osakechan/notoriousPID/img/LCD/nPIDmenu.jpg

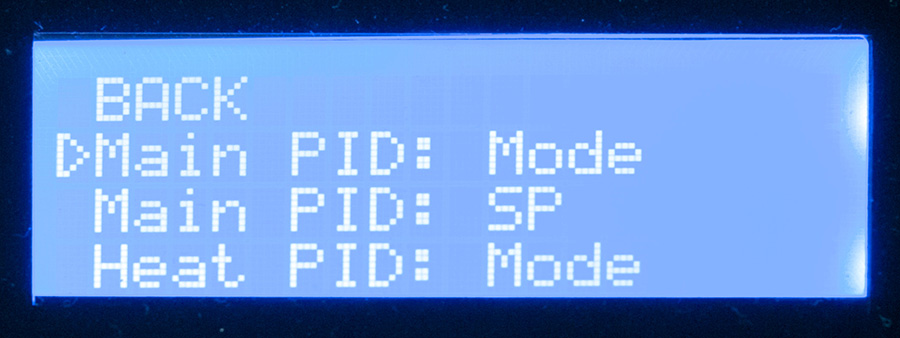
img/LCD/nPIDmenu.jpg
