osakechan/notoriousPID/img/LCD/nPIDmenuPGM.jpg

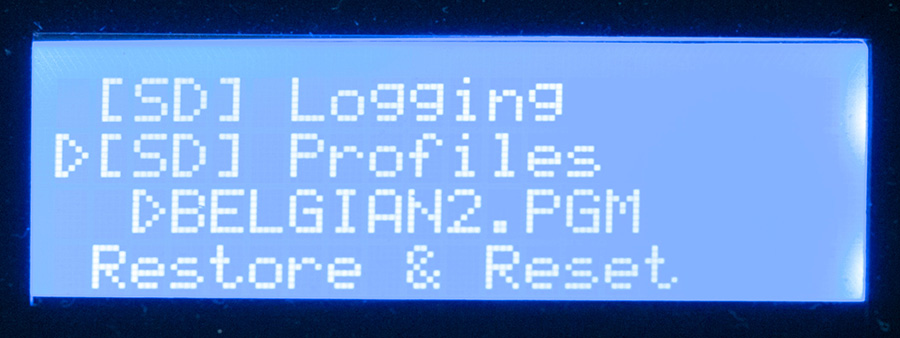
img/LCD/nPIDmenuPGM.jpg
