osakechan/notoriousPID/img/LCD/nPIDmenuUNIT.jpg

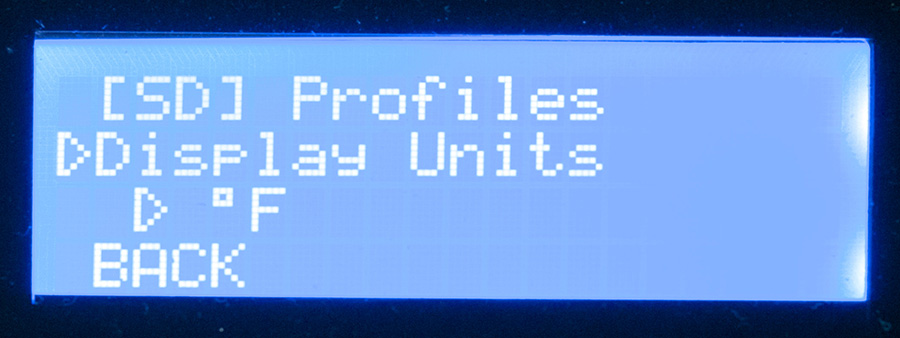
img/LCD/nPIDmenuUNIT.jpg
