osakechan/notoriousPID/img/LCD/nPIDpage1.jpg

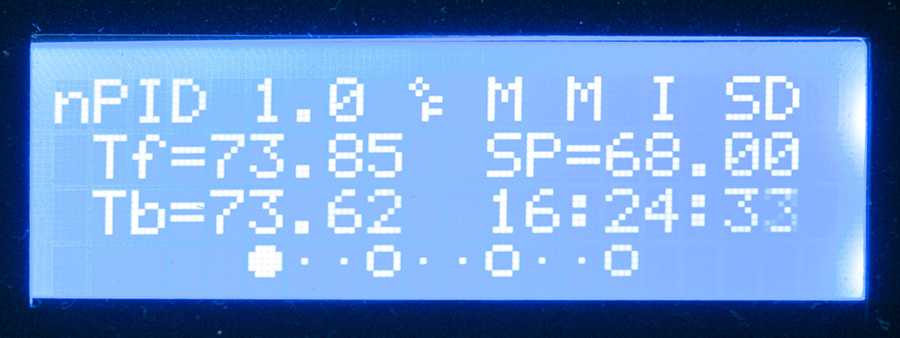
img/LCD/nPIDpage1.jpg
