osakechan/notoriousPID/img/LCD/nPIDpage2.jpg

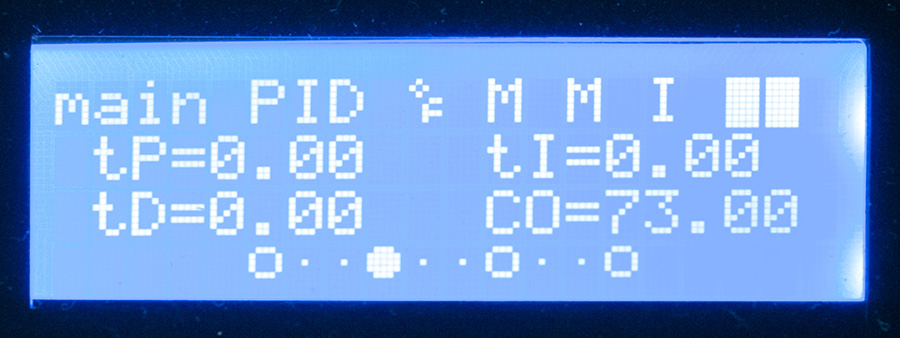
img/LCD/nPIDpage2.jpg
