osakechan/notoriousPID/img/LCD/nPIDpage3.jpg

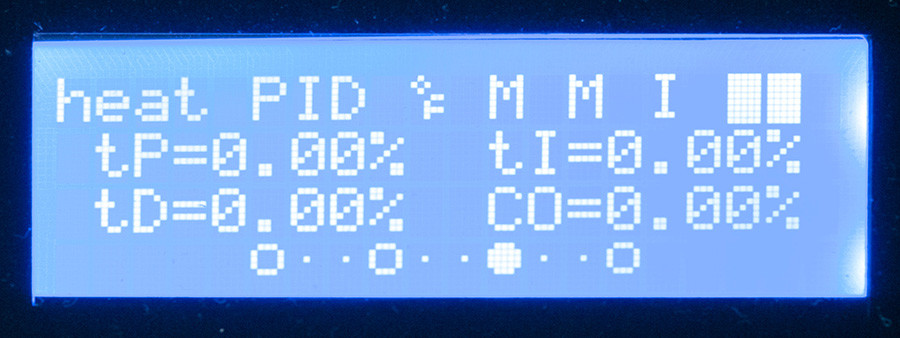
img/LCD/nPIDpage3.jpg
