osakechan/notoriousPID/img/LCD/nPIDpage4.jpg

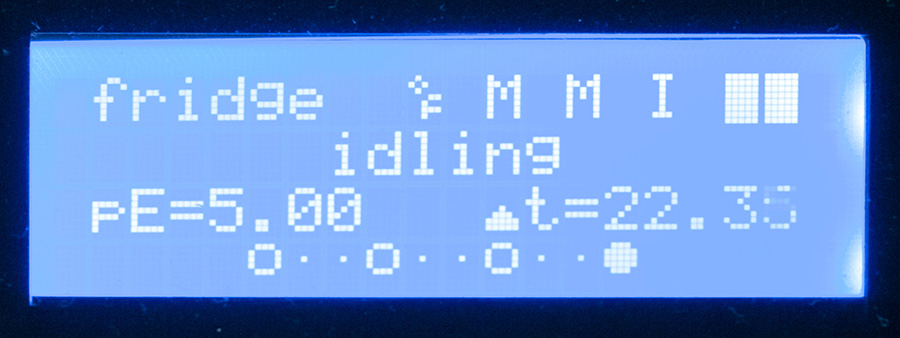
img/LCD/nPIDpage4.jpg
