osakechan/notoriousPID/img/BUILD/fermentation_space.jpg

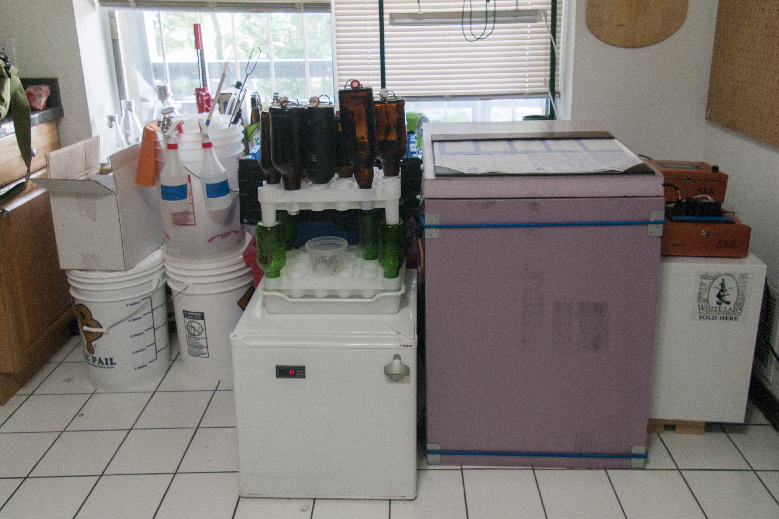
img/BUILD/fermentation_space.jpg
